d3distef/SprintBeaconLidarESP32/secrets.h

#line 1 "C:\\Users\\d3dis\\Documents\\Arduino\\SprintBeaconLidarOnlyFInalWorkingVersion1.0\\secrets.h"
// secrets.h  -- DO NOT COMMIT THIS FILE
#pragma once

// Wi-Fi (STA)
const char* WIFI_SSID = "CXNK01889B9F 2.4G";
const char* WIFI_PASS = "dd47e5e052f134e3";

// Optional: OTA password (uncomment to enable)
// #define OTA_PASS "choose-a-strong-password"
